TinyCircuits/TinyCircuits-TinyZero-ASM2021/cad/TinyZero_ASM2001_REV5-DETAILED_DRAWING_COMPACT-PNG.png

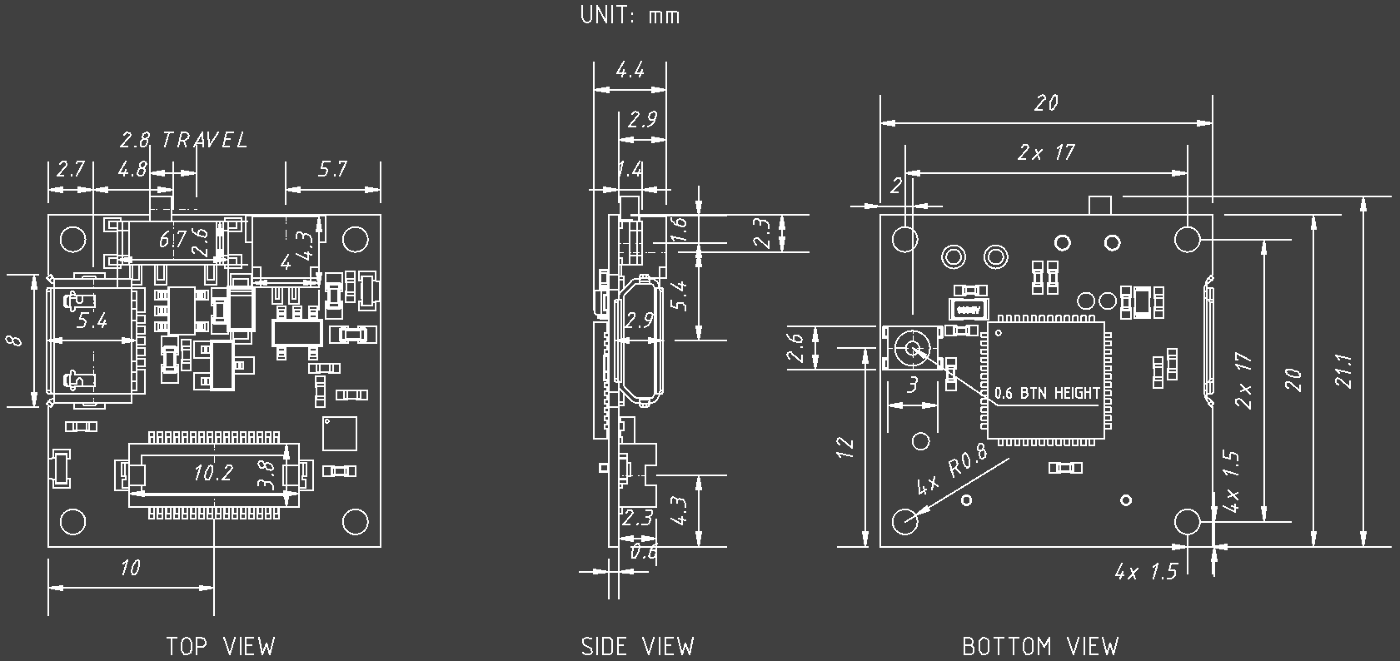
cad/TinyZero_ASM2001_REV5-DETAILED_DRAWING_COMPACT-PNG.png
