TinyCircuits/TinyCircuits-TinyZero-ASM2021/images/TinyZero_back.jpg

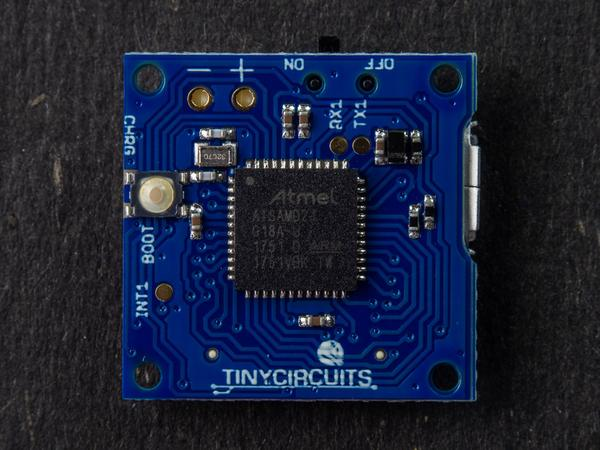
images/TinyZero_back.jpg
