TinyCircuits/TinyCircuits-TinyZero-ASM2021/images/TinyZero_BMA250_present.jpg

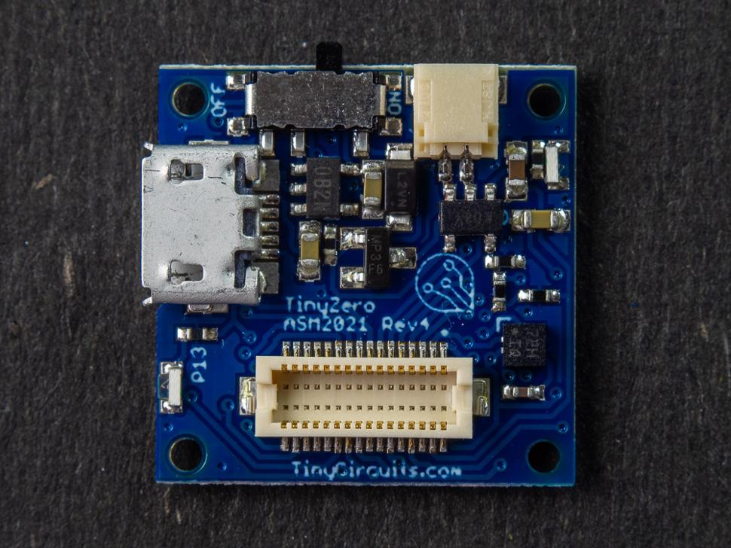
images/TinyZero_BMA250_present.jpg
