TinyCircuits/TinyCircuits-TinyZero-ASM2021/images/TinyZeroBack_labels.png

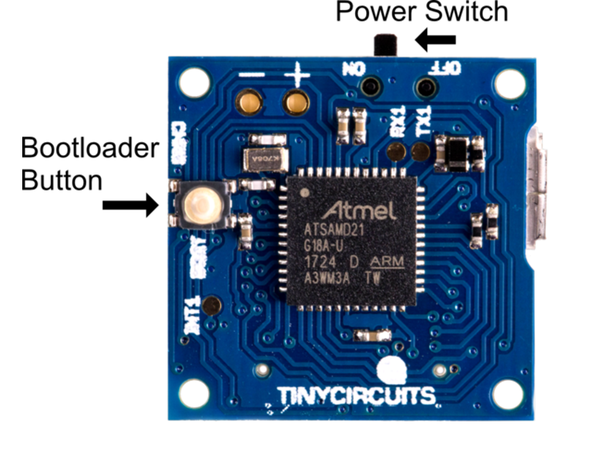
images/TinyZeroBack_labels.png
