TinyCircuits/TinyCircuits-TinyZero-ASM2021/images/TinyZeroFront_labels.png

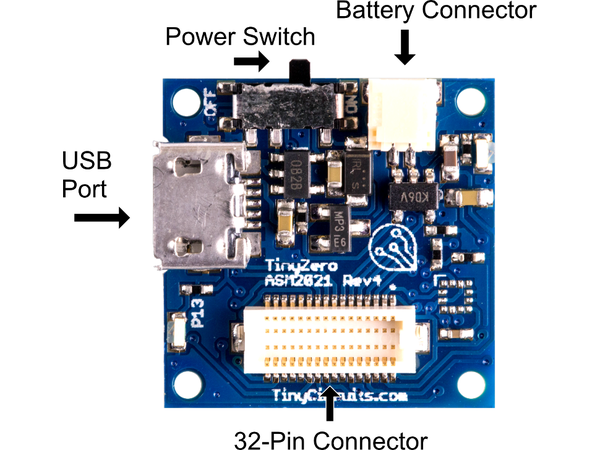
images/TinyZeroFront_labels.png
