TinyCircuits/TinyCircuits-TinyZero-ASM2021/images/Accel_Cayenne_Tutorial/cayenne_empty_dash.png

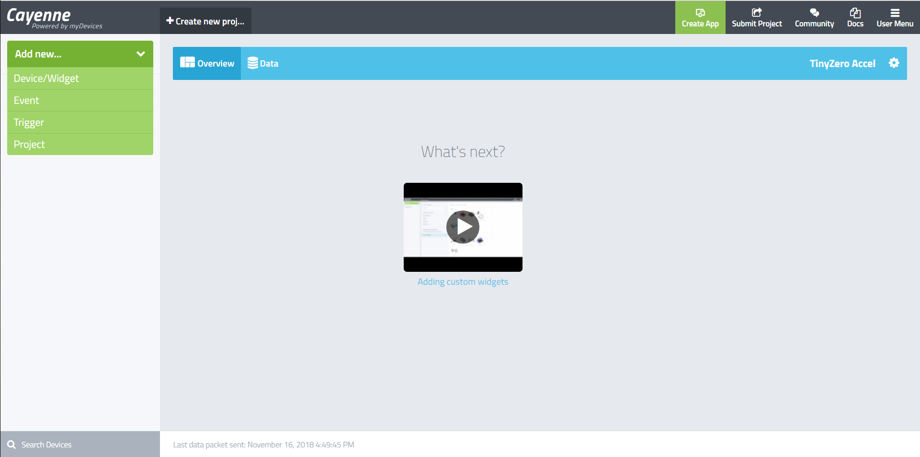
images/Accel_Cayenne_Tutorial/cayenne_empty_dash.png
