TinyCircuits/TinyCircuits-TinyZero-ASM2021/images/Accel_Cayenne_Tutorial/cayenne_signup.png

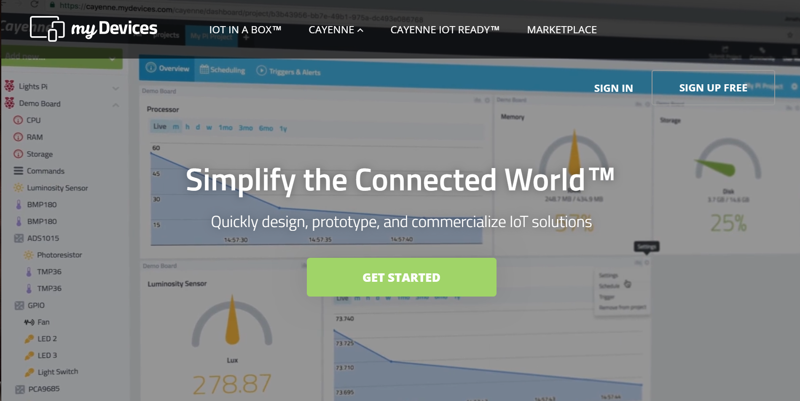
images/Accel_Cayenne_Tutorial/cayenne_signup.png
