TinyCircuits/TinyCircuits-TinyZero-ASM2021/images/Accel_Cayenne_Tutorial/channels_cayenne.png

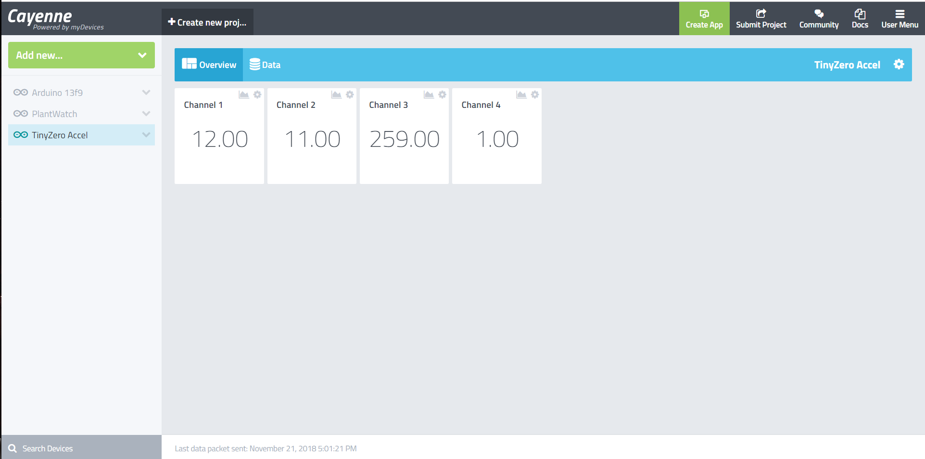
images/Accel_Cayenne_Tutorial/channels_cayenne.png
