TinyCircuits/TinyCircuits-TinyZero-ASM2021/images/Accel_Cayenne_Tutorial/tools_selections.png

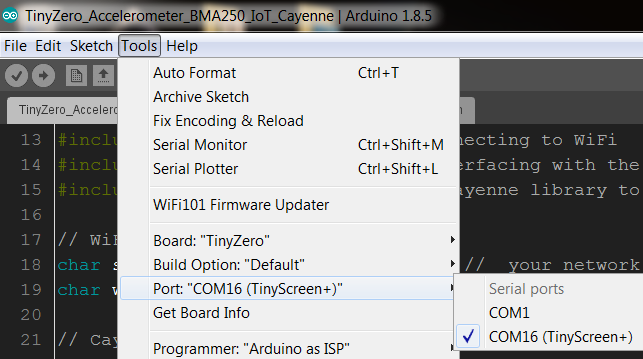
images/Accel_Cayenne_Tutorial/tools_selections.png
