TinyCircuits/TinyCircuits-TinyZero-ASM2021/images/Accelerometer_Usage_Tutorial/accel_plotted_grande.png

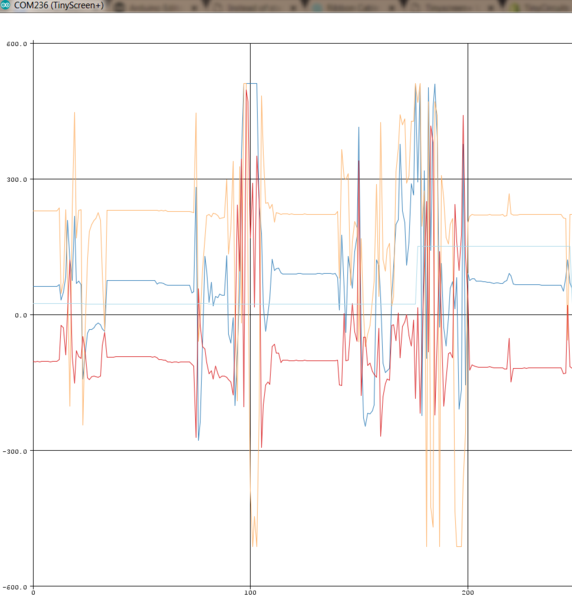
images/Accelerometer_Usage_Tutorial/accel_plotted_grande.png
