TinyCircuits/TinyCircuits-TinyZero-ASM2021/images/Accelerometer_Usage_Tutorial/tinyzero_grande.png

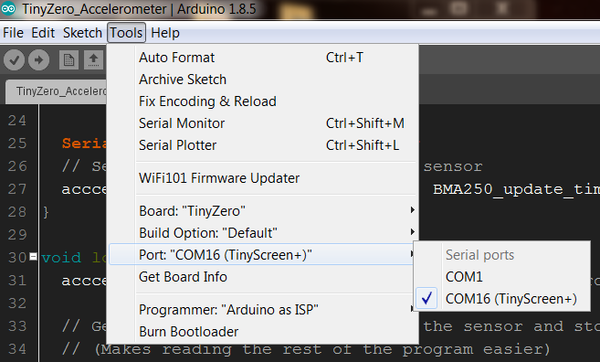
images/Accelerometer_Usage_Tutorial/tinyzero_grande.png
