TinyCircuits/TinyCircuits-TinyZero-ASM2021/images/ASM2021-R-Tutorial-Image-01.jpg

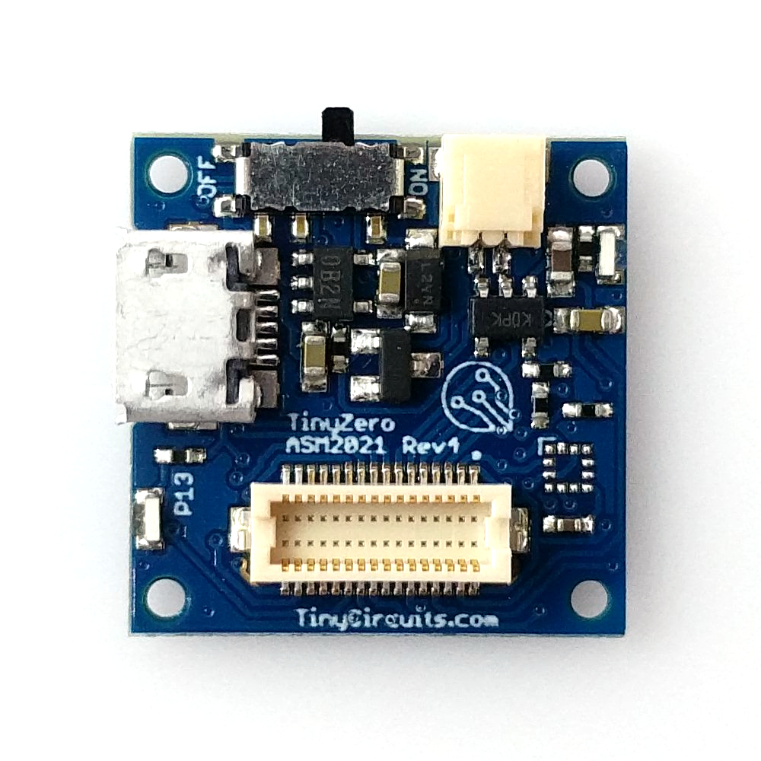
images/ASM2021-R-Tutorial-Image-01.jpg
