TinyCircuits/TinyCircuits-TinyZero-ASM2021/images/ASM2021-R-Tutorial-Image-01.png

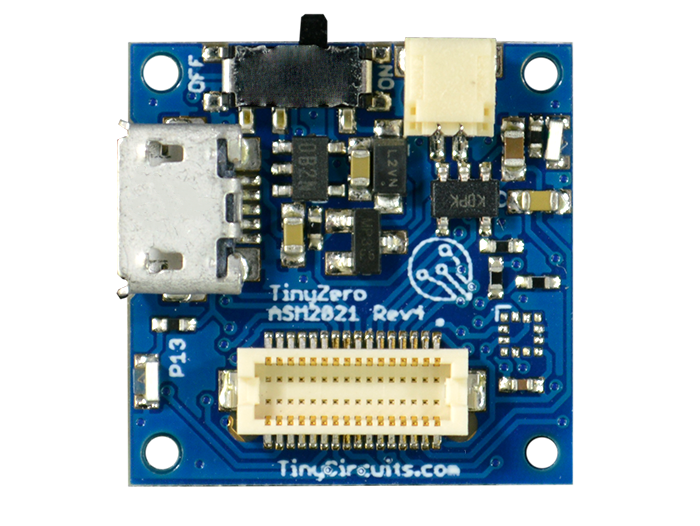
images/ASM2021-R-Tutorial-Image-01.png
