TinyCircuits/TinyCircuits-TinyZero-ASM2021/images/tutorial_images/ASM2021-Tutorial-Picture-12.png

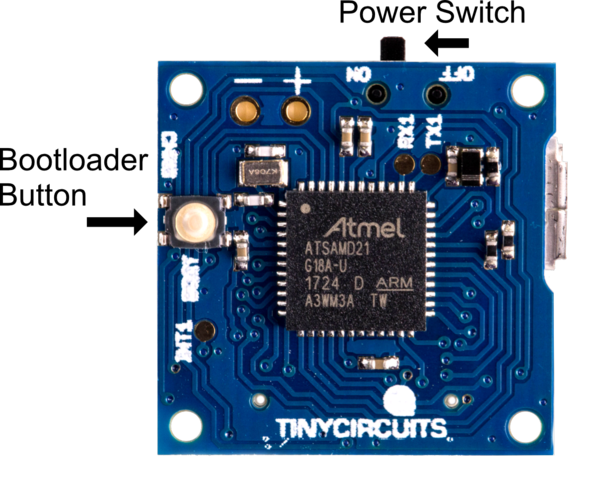
images/tutorial_images/ASM2021-Tutorial-Picture-12.png
